BlackAlps/blackalps-19-badge/badgeOS/apps/ph0wnapp.py

import machine
import ssd1306
import framebuf


class App:
    def __init__(self, badge):
        self.badge = badge
        self.NAME = "Ph0wn"

    def run(self):
        ph0wn = bytearray(b'\xff\xff\xff\xff\xff\xff\xff\xff\xff\xff\xff\xff\xff\xff\xff\xff\xff\xff\xff\xff\xff\xff\xff\xff\xff\xff\xff\xff\xff\xff\xff\xff\xff\xff\xff\xff\xff\xff\xff\xff\xff\xff\xff\xff\xff\xff\xff\xff\xff\xff\xff\xff\xff\xff\xff\xff\xff\xff\xff\xff\xff\xff\xff\xff\xff\xff\xff\xff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
        i2c = machine.I2C(scl=machine.Pin(27), sda=machine.Pin(26))
        oled = ssd1306.SSD1306_I2C(128, 64, i2c, 0x3c)
        self.badge.screen.clear()
        fb = framebuf.FrameBuffer(ph0wn, 128, 64, framebuf.MVLSB)
        oled.blit(fb, 0,0)
        oled.show()
        self.badge.buttons.wait_button()
