BlackAlps/blackalps-19-badge/badgeOS/apps/picolecroco.py

import machine
import ssd1306
import framebuf

# This app shows Pico Le Croco

class App:
    def __init__(self, badge):
        self.badge = badge
        self.NAME = "Pico"

    def run(self):
        pico = bytearray(b'\x00\x00\x00\x00\x00\x00\x00\x00\x00\x00\x00\x00\x00\x00\x00\x00\x00\x00\x00\x00\x00\x00\xa0\x80\x10\x08\x00\x00\x04\x04\x04\x80\x00\x00\x00\x04\x08\xe0\x00\x00\x00\x00\x00\x00\x00\x00\x00\x00\x00\xc0 \x10\x08\x00\x04\x04\x00\x80B\x82"BR\x12\x02\x02J\n\x8a\n\x02\x02\x12\x0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
        i2c = machine.I2C(scl=machine.Pin(27), sda=machine.Pin(26))
        oled = ssd1306.SSD1306_I2C(128, 64, i2c, 0x3c)
        self.badge.screen.clear()
        fb = framebuf.FrameBuffer(pico, 128, 64, framebuf.MVLSB)
        oled.blit(fb, 0,0)
        oled.show()
        self.badge.buttons.wait_button()
